Dholydai/The_Post-Mech_Praxis/KB_Stl_Gen/left-post-mech.png

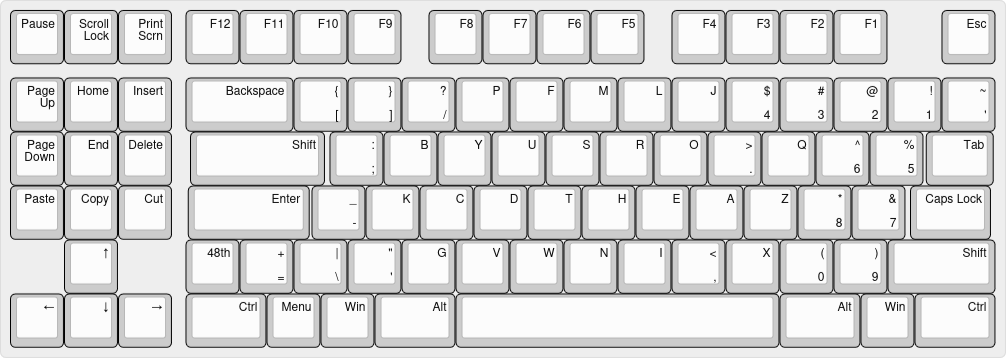
KB_Stl_Gen/left-post-mech.png
