Dholydai/The_Post-Mech_Praxis/KB_Stl_Gen/post-mech.png

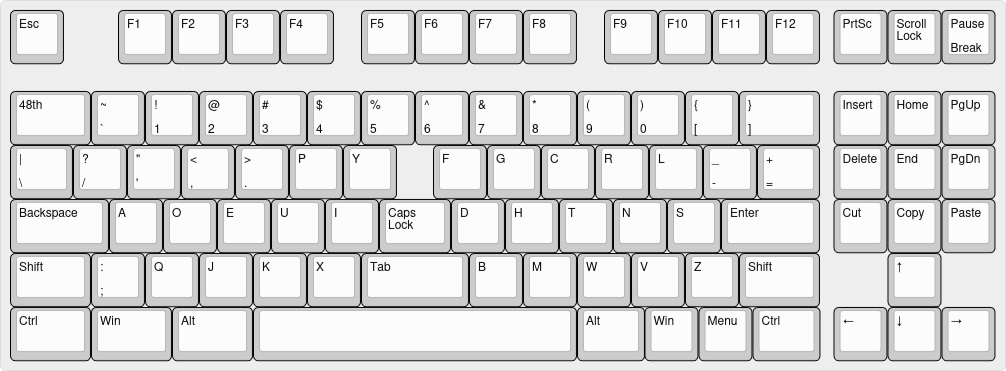
KB_Stl_Gen/post-mech.png
