Dholydai/The_Post-Mech_Praxis/KB_Stl_Gen/right-post-mech.png

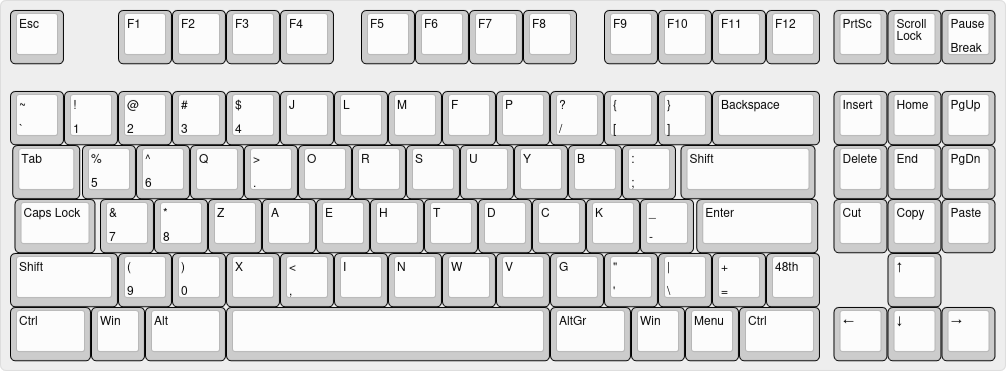
KB_Stl_Gen/right-post-mech.png
