Dholydai/The_Post-Mech_Praxis/Z4/Draw/A1PolDv-1.0.png

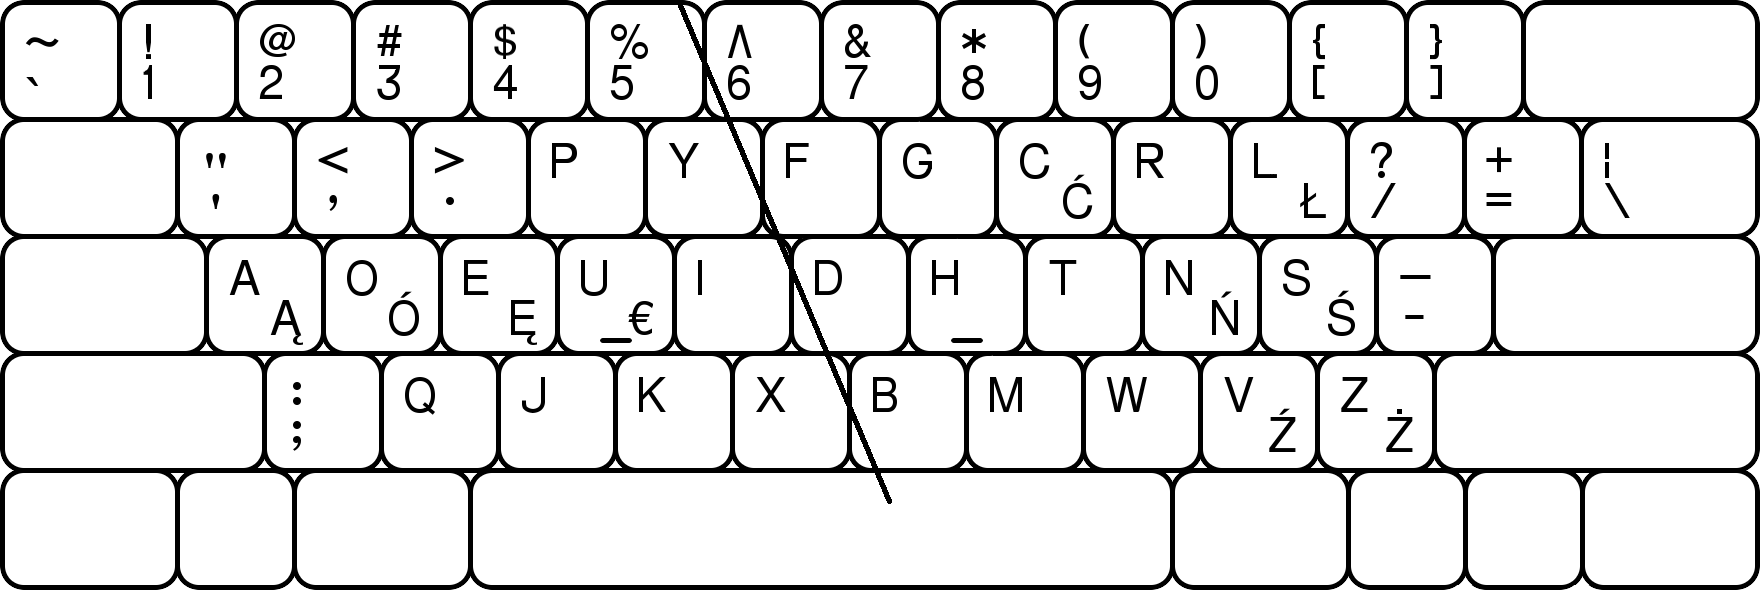
Z4/Draw/A1PolDv-1.0.png
