Dholydai/The_Post-Mech_Praxis/Z4/Draw/A3Russ-2.1.jpg

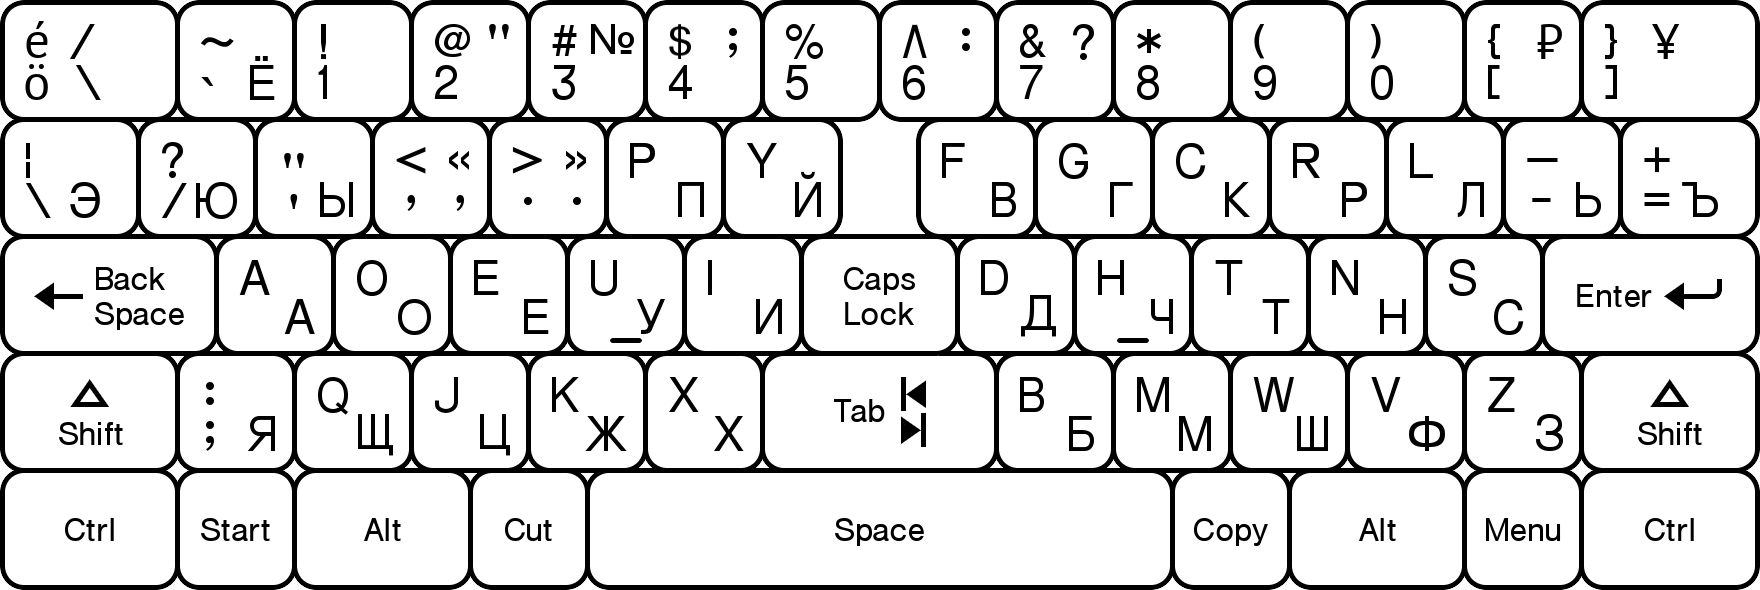
Z4/Draw/A3Russ-2.1.jpg
