Dholydai/The_Post-Mech_Praxis/Z4/Draw/A4Hung-1.0.jpg

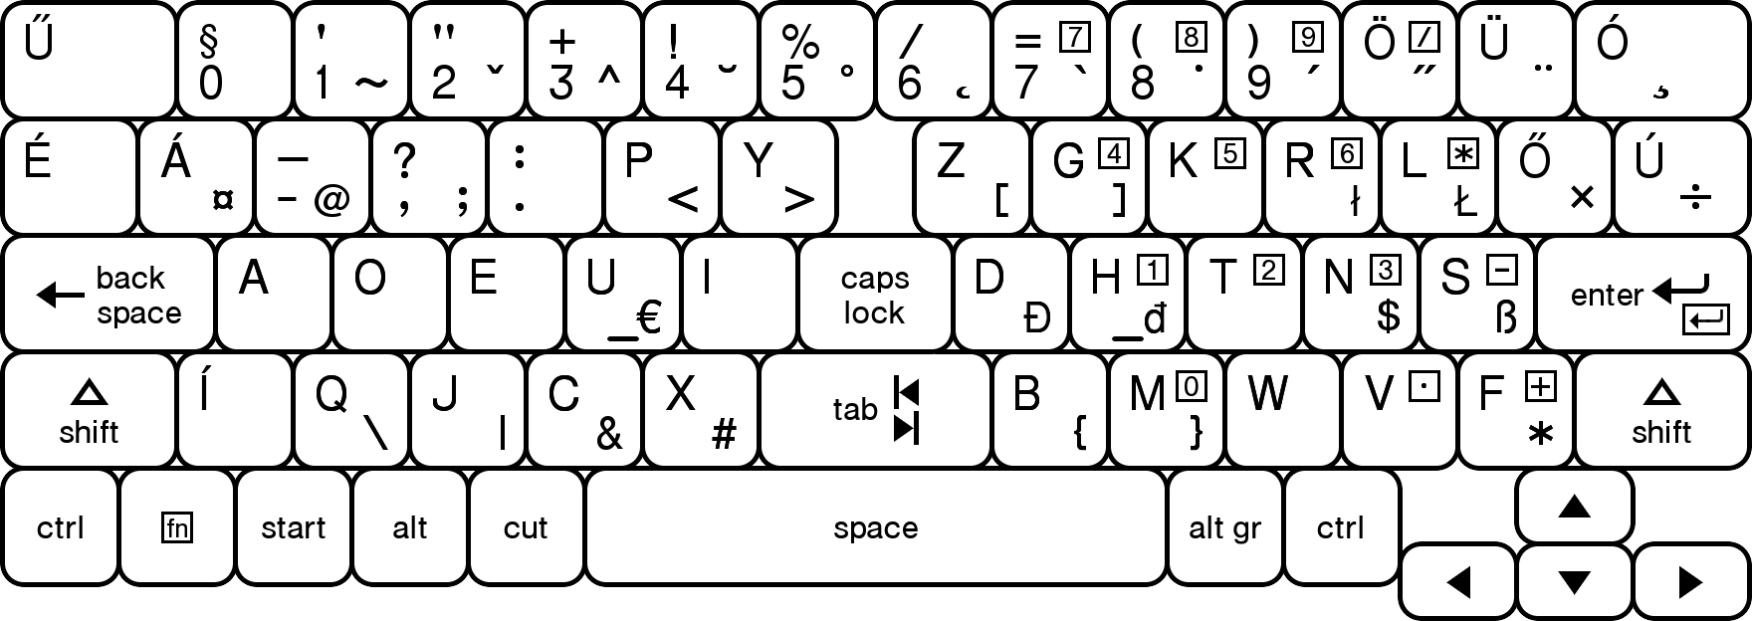
Z4/Draw/A4Hung-1.0.jpg
