Dholydai/The_Post-Mech_Praxis/Z4/Draw/X1US-1.0.jpg

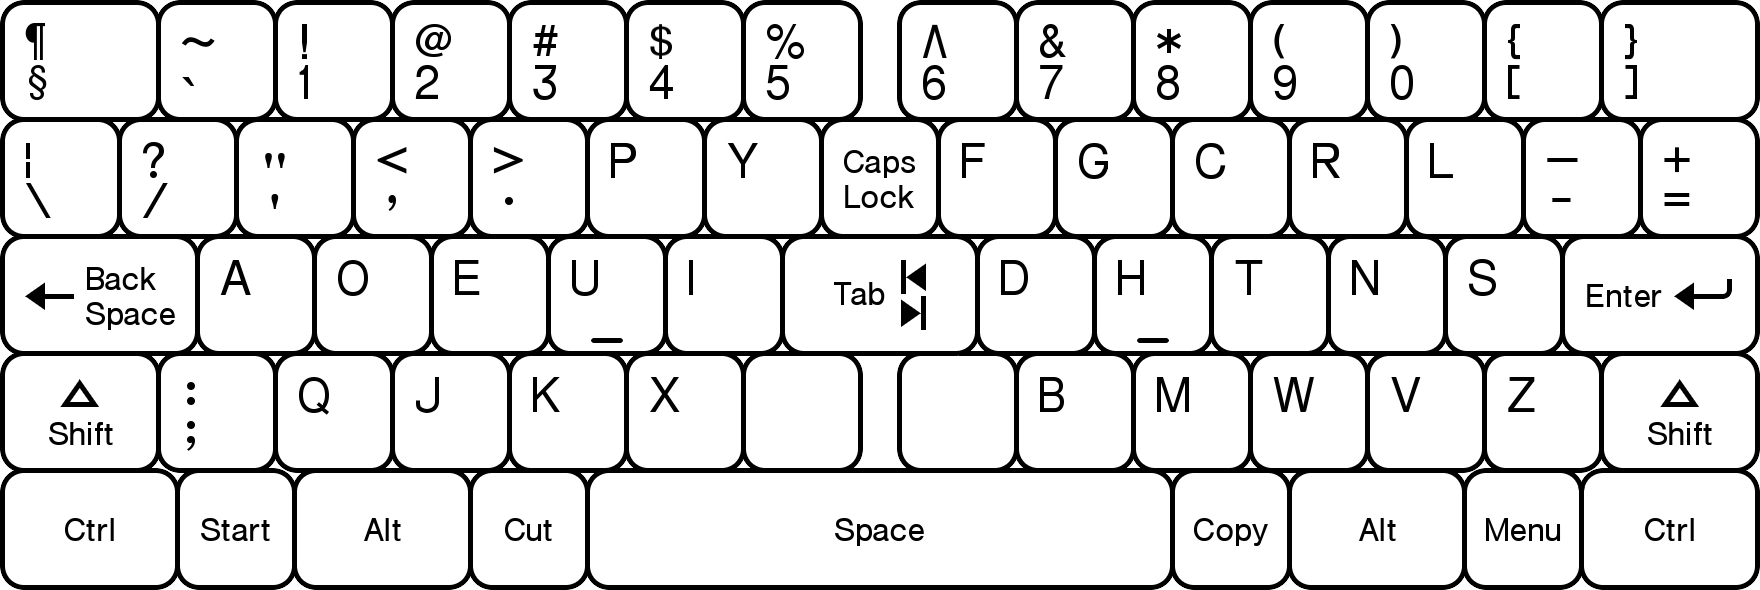
Z4/Draw/X1US-1.0.jpg
